malcx95/ZeKeyboard/firmware/ledsv3.h

#ifndef LEDSV3_H 
#define LEDSV3_H

#include <stdint.h>

typedef uint8_t led_t;

//*********************************
// ROW 0
//*********************************

const led_t LED_LOGO =            0;
const led_t LED_F12 =             1;
const led_t LED_F11 =             2;
const led_t LED_F10 =             3;
const led_t LED_F9 =              4;
const led_t LED_F8 =              5;
const led_t LED_F7 =              6;
const led_t LED_F6 =              7;
const led_t LED_F5 =              8;
const led_t LED_F4 =              9;
const led_t LED_F3 =              10;
const led_t LED_F2 =              11;
const led_t LED_F1 =              12;
const led_t LED_ESC =             13;

//*****************************
// ROW 1
//*****************************

const led_t LED_TILDE =           14;
const led_t LED_1 =               15;
const led_t LED_2 =               16;
const led_t LED_3 =               17;
const led_t LED_4 =               18;
const led_t LED_5 =               19;
const led_t LED_6 =               20;
const led_t LED_7 =               21;
const led_t LED_8 =               22;
const led_t LED_9 =               23;
const led_t LED_0 =               24;
const led_t LED_MINUS =           25;
const led_t LED_EQUAL =           26;
const led_t LED_BACKSPACE =       27;
const led_t LED_MACRO1 =          28;
const led_t LED_NUMLOCK =         29;
const led_t LED_NUMPAD_SLASH =    30;
const led_t LED_NUMPAD_ASTERISK = 31;
const led_t LED_NUMPAD_MINUS =    32;

//*****************************
// ROW 2
//*****************************

const led_t LED_NUMPAD_PLUS =    33;
const led_t LED_NUMPAD_9 =       34;
const led_t LED_NUMPAD_8 =       35;
const led_t LED_NUMPAD_7 =       36;
const led_t LED_MACRO2 =         37;
const led_t LED_BACKSLASH =      38;
const led_t LED_RIGHT_BRACE =    39;
const led_t LED_LEFT_BRACE =     40;
const led_t LED_P =              41;
const led_t LED_O =              42;
const led_t LED_I =              43;
const led_t LED_U =              44;
const led_t LED_Y =              45;
const led_t LED_T =              46;
const led_t LED_R =              47;
const led_t LED_E =              48;
const led_t LED_W =              49;
const led_t LED_Q =              50;
const led_t LED_TAB =            51;

//*****************************
// ROW 3
//*****************************

const led_t LED_FN =             52;
const led_t LED_A =              53;
const led_t LED_S =              54;
const led_t LED_D =              55;
const led_t LED_F =              56;
const led_t LED_G =              57;
const led_t LED_H =              58;
const led_t LED_J =              59;
const led_t LED_K =              60;
const led_t LED_L =              61;
const led_t LED_SEMICOLON =      62;
const led_t LED_QUOTE =          63;
const led_t LED_ENTER =          64;
const led_t LED_MACRO3 =         65;
const led_t LED_NUMPAD_4 =       66;
const led_t LED_NUMPAD_5 =       67;
const led_t LED_NUMPAD_6 =       68;

//*****************************
// ROW 4
//*****************************

const led_t LED_NUMPAD_ENTER =   69;
const led_t LED_NUMPAD_3 =       70;
const led_t LED_NUMPAD_2 =       71;
const led_t LED_NUMPAD_1 =       72;
const led_t LED_MACRO4 =         73;
const led_t LED_EXTRA =          74;
const led_t LED_UP =             75;
const led_t LED_SLASH =          76;
const led_t LED_PERIOD =         77;
const led_t LED_COMMA =          78;
const led_t LED_M =              79;
const led_t LED_N =              80;
const led_t LED_B =              81;
const led_t LED_V =              82;
const led_t LED_C =              83;
const led_t LED_X =              84;
const led_t LED_Z =              85;
const led_t LED_NON_US_BS =      86;
const led_t LED_LSHIFT =         87;

//*****************************
// ROW 5
//*****************************

const led_t LED_LEFT_CTRL =      88;
const led_t LED_LEFT_SUPER =     89;
const led_t LED_ALT =            90;
const led_t LED_SPACE_LEFT =     91;
const led_t LED_SPACE_MAIN =     92;
const led_t LED_SPACE_RIGHT =    93;
const led_t LED_ALTGR =          94;
const led_t LED_LEFT =           95;
const led_t LED_DOWN =           96;
const led_t LED_RIGHT =          97;
const led_t LED_MACRO5 =         98;
const led_t LED_NUMPAD_0 =       99;
const led_t LED_NUMPAD_PERIOD =  100;


#endif
