malcx95/ZeKeyboard/firmware/ledsfull.h

#ifndef LEDSFULL_H 
#define LEDSFULL_H 

#include <stdint.h>

typedef uint8_t led_t;

//*********************************
// ROW 5
//*********************************

const led_t LED_NUMPAD_PERIOD = 0;
const led_t LED_NUMPAD_0 = 1;
const led_t LED_RIGHT = 2;
const led_t LED_DOWN = 3;
const led_t LED_LEFT = 4;
const led_t LED_RIGHT_CTRL = 5;
const led_t LED_RIGHT_FN = 6;
const led_t LED_RIGHT_SUPER = 7;
const led_t LED_ALTGR = 8;
const led_t LED_SPACE = 9;
const led_t LED_ALT = 10;
const led_t LED_LEFT_SUPER = 11;
const led_t LED_LEFT_CTRL = 12;

//*****************************
// ROW 4
//*****************************

const led_t LED_LSHIFT = 13;
const led_t LED_NON_US_BS = 14;
const led_t LED_Z = 15;
const led_t LED_X = 16;
const led_t LED_C = 17;
const led_t LED_V = 18;
const led_t LED_B = 19;
const led_t LED_N = 20;
const led_t LED_M = 21;
const led_t LED_COMMA = 22;
const led_t LED_PERIOD = 23;
const led_t LED_SLASH = 24;
const led_t LED_RSHIFT = 25;
const led_t LED_UP = 26;
const led_t LED_NUMPAD_1 = 27;
const led_t LED_NUMPAD_2 = 28;
const led_t LED_NUMPAD_3 = 29;
const led_t LED_NUMPAD_ENTER = 30;

//*****************************
// ROW 3
//*****************************

const led_t LED_NUMPAD_6 = 31;
const led_t LED_NUMPAD_5 = 32;
const led_t LED_NUMPAD_4 = 33;
const led_t LED_ENTER = 34;
const led_t LED_BACKSLASH = 35;
const led_t LED_QUOTE = 36;
const led_t LED_SEMICOLON = 37;
const led_t LED_L = 38;
const led_t LED_K = 39;
const led_t LED_J = 40;
const led_t LED_H = 41;
const led_t LED_G = 42;
const led_t LED_F = 43;
const led_t LED_D = 44;
const led_t LED_S = 45;
const led_t LED_A = 46;
const led_t LED_FN = 47;

//*****************************
// ROW 2
//*****************************

const led_t LED_TAB = 48;
const led_t LED_Q = 49;
const led_t LED_W = 50;
const led_t LED_E = 51;
const led_t LED_R = 52;
const led_t LED_T = 53;
const led_t LED_Y = 54;
const led_t LED_U = 55;
const led_t LED_I = 56;
const led_t LED_O = 57;
const led_t LED_P = 58;
const led_t LED_LEFT_BRACE = 59;
const led_t LED_RIGHT_BRACE = 60;
const led_t LED_DEL = 61;
const led_t LED_END = 62;
const led_t LED_PGDOWN = 63;
const led_t LED_NUMPAD_7 = 64;
const led_t LED_NUMPAD_8 = 65;
const led_t LED_NUMPAD_9 = 66;
const led_t LED_NUMPAD_PLUS = 67;

//*****************************
// ROW 1
//*****************************

const led_t LED_NUMPAD_MINUS = 68;
const led_t LED_NUMPAD_ASTERISK = 69;
const led_t LED_NUMPAD_SLASH = 70;
const led_t LED_NUMLOCK = 71;
const led_t LED_PGUP = 72;
const led_t LED_HOME = 73;
const led_t LED_INSERT = 74;
const led_t LED_BACKSPACE = 75;
const led_t LED_EQUAL = 76;
const led_t LED_MINUS = 77;
const led_t LED_0 = 78;
const led_t LED_9 = 79;
const led_t LED_8 = 80;
const led_t LED_7 = 81;
const led_t LED_6 = 82;
const led_t LED_5 = 83;
const led_t LED_4 = 84;
const led_t LED_3 = 85;
const led_t LED_2 = 86;
const led_t LED_1 = 87;
const led_t LED_TILDE = 88;

//*****************************
// ROW 0
//*****************************

const led_t LED_ESC = 89;
const led_t LED_F1 = 90;
const led_t LED_F2 = 91;
const led_t LED_F3 = 92;
const led_t LED_F4 = 93;
const led_t LED_F5 = 94;
const led_t LED_F6 = 95;
const led_t LED_F7 = 96;
const led_t LED_F8 = 97;
const led_t LED_F9 = 98;
const led_t LED_F10 = 99;
const led_t LED_F11 = 100;
const led_t LED_F12 = 101;
const led_t LED_PRINTSCREEN = 102;
const led_t LED_SCROLL_LOCK = 103;
const led_t LED_PAUSE = 104;
const led_t LED_EXTRA1 = 105;
const led_t LED_EXTRA2 = 106;
const led_t LED_EXTRA3 = 107;
const led_t LED_EXTRA4 = 108;

#endif
